CropSentry/Hardware/sch-files/CropSentry.kicad_sch

## KiCad design sch-files/CropSentry.kicad_sch (2026-09-28)

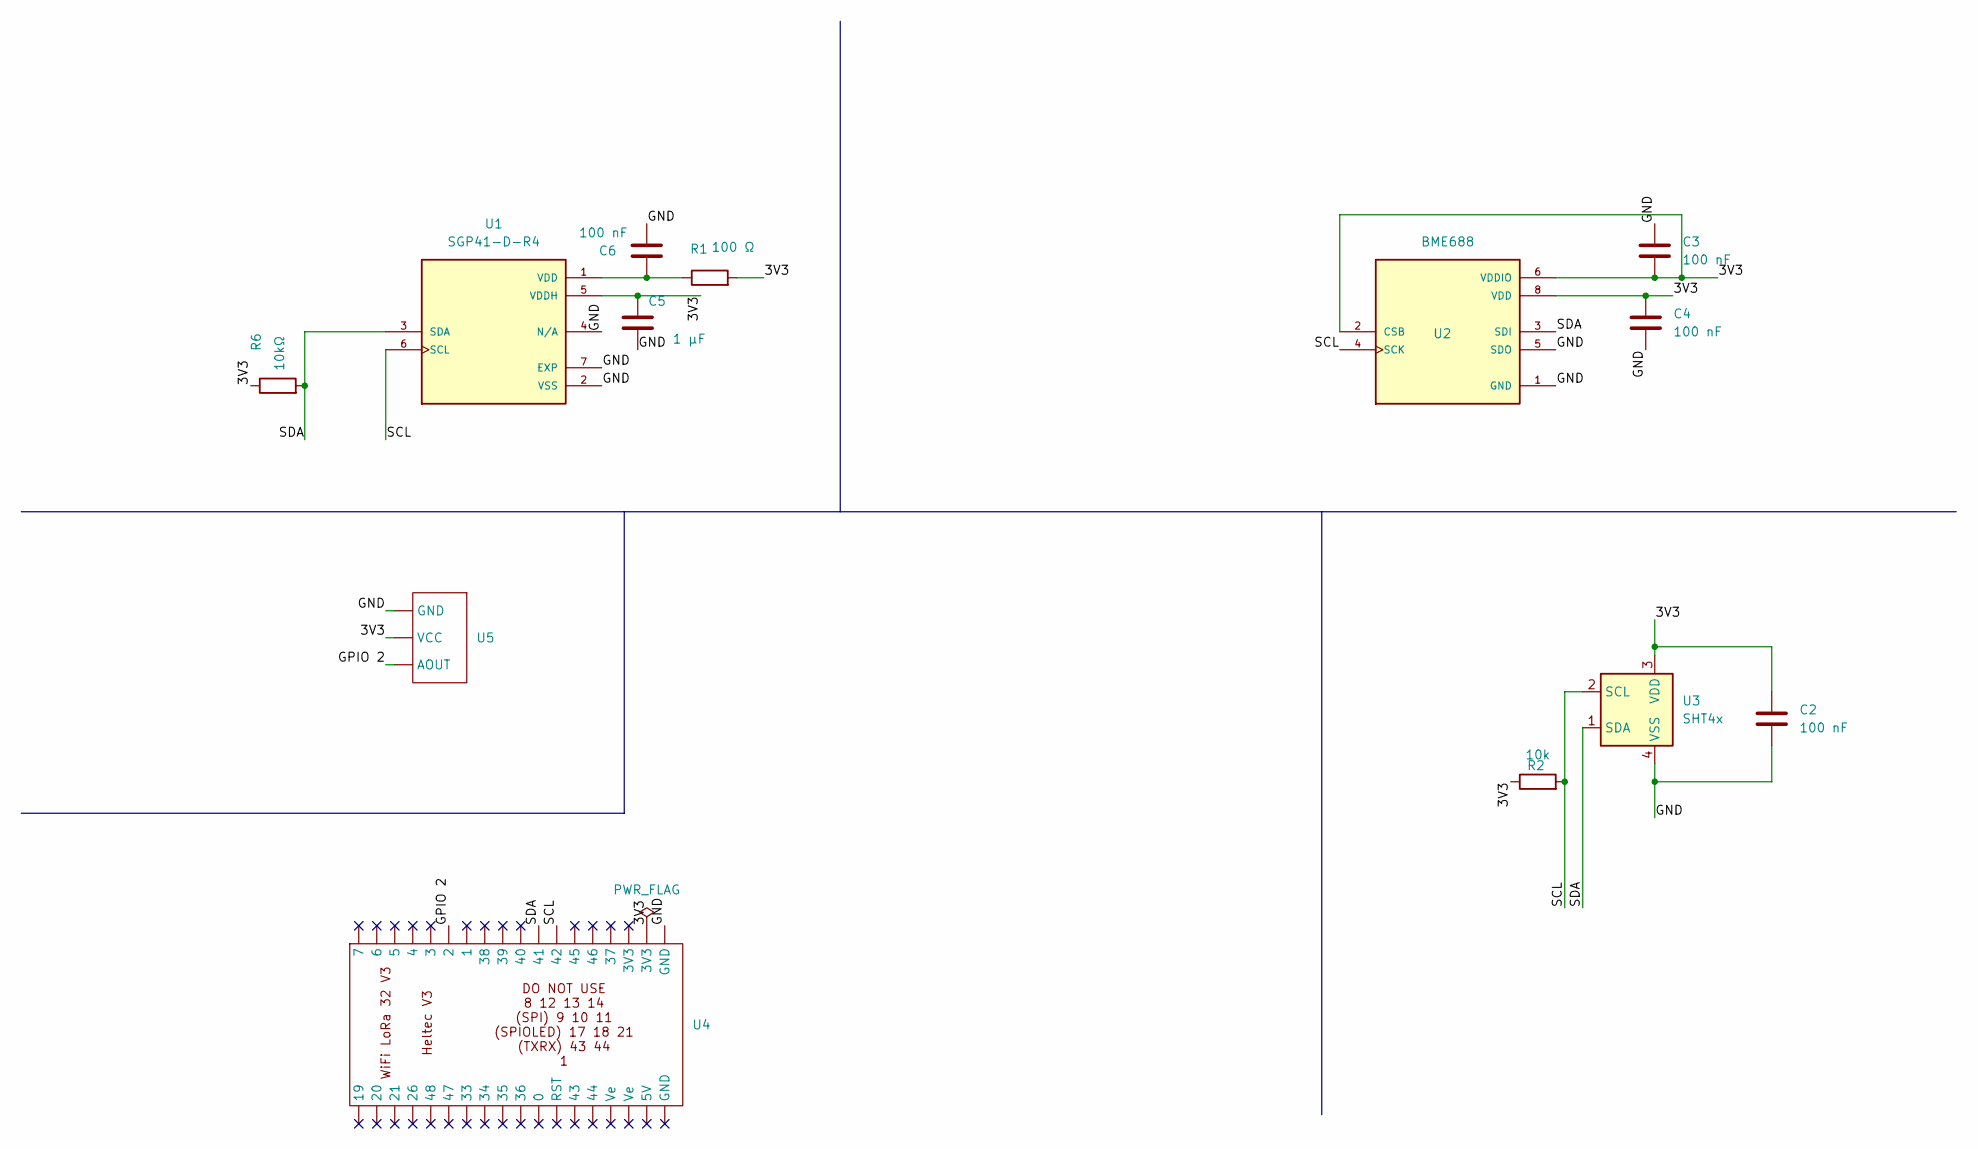
[picture p64: schematic CropSentry.kicad_sch]

Parts:
C2, C3, C4, C6: 100 nF
C5: 1 µF; C_0805_2012Metric
R1: 100 Ω
R2: 10k
R6: 10kΩ
U1: SGP41-D-R4; XDCR_SGP41-D-R4; PARTREV 1.0
U2: BME688; IC_BME688; PARTREV 1.0
U3: SHT4x; Sensirion_DFN-4_1.5x1.5mm_P0.8mm_SHT4x_NoCentralPad
U4, U5: (no value)

Connections:
3V3: C2.2, C3.1, C4.2, C5.2, R1.2, R2.1, R6.1, U1.5 (VDDH), U2.2 (CSB), U2.6 (VDDIO), U2.8 (VDD), U3.3 (VDD), U4., U5.
GND: C2.1, C3.2, C4.1, C5.1, C6.2, U1.2 (VSS), U1.4 (N/A), U1.7 (EXP), U2.1 (GND), U2.5 (SDO), U2.7 (GND), U3.4 (VSS), U4., U5.
GPIO 2: U4., U5.
unnamed: C6.1, R1.1, U1.1 (VDD)
SCL: R2.2, U1.6 (SCL), U2.4 (SCK), U3.2 (SCL), U4.
SDA: R6.2, U1.3 (SDA), U2.3 (SDI), U3.1 (SDA), U4.
